FriendTeamInc/JukeBox/desktop/src/config.rs

// Config

use std::{
    collections::HashMap,
    fs::{File, create_dir_all},
    path::PathBuf,
};

use jukebox_util::{peripheral::DeviceType, rgb::RgbProfile, screen::ScreenProfile};
use serde::{Deserialize, Serialize};
use uuid::Uuid;

use crate::{
    actions::{meta::MetaNoAction, types::Action},
    input::InputKey,
};

#[derive(Serialize, Deserialize, Clone, PartialEq)]
pub enum ActionIcon {
    ImageIcon(String),
    DefaultActionIcon,
}

#[derive(Serialize, Deserialize, Clone)]
pub struct ActionConfig {
    pub action: Action,
    pub icons: Vec<ActionIcon>,
}
impl Default for ActionConfig {
    fn default() -> Self {
        Self {
            action: Box::new(MetaNoAction::default()),
            icons: Default::default(),
        }
    }
}
impl PartialEq for ActionConfig {
    fn eq(&self, other: &Self) -> bool {
        self.action == other.action.clone() && self.icons == other.icons
    }
}

#[derive(Serialize, Deserialize, Clone)]
pub struct DeviceConfig {
    pub key_map: HashMap<InputKey, ActionConfig>,
    pub rgb_profile: Option<RgbProfile>,
    pub screen_profile: Option<ScreenProfile>,
}

#[derive(Serialize, Deserialize, Clone)]
pub struct DeviceInfo {
    pub device_type: DeviceType,
    pub nickname: String,
}

#[derive(Serialize, Deserialize, Clone)]
pub struct ProfileConfig {
    // pub profile_uuid: String,
    pub profile_name: String,
    pub device_configs: HashMap<String, DeviceConfig>,
}

#[derive(Serialize, Deserialize, Clone)]
pub struct JukeBoxConfig {
    // Profile Name -> Device UID -> Device Config
    // TODO: change profile name to uuid, store name in a separate variable
    pub profiles: HashMap<String, ProfileConfig>,

    // Device UID -> (Device Type, Device Nickname)
    pub devices: HashMap<String, DeviceInfo>,

    // Action Module ID -> Action Module Config
    pub action_module_config: HashMap<String, HashMap<String, String>>,

    // Profile Name
    // TODO: change profile name to uuid, store name in a separate variable
    pub current_profile: String,

    pub enable_splash: bool,
    pub always_save_on_exit: bool,
    pub ignore_update_notifications: bool,

    pub seen_intro_messages: bool,
}
impl Default for JukeBoxConfig {
    fn default() -> Self {
        let uuid = Uuid::new_v4().to_string();

        JukeBoxConfig {
            profiles: HashMap::from([(
                uuid.clone(),
                ProfileConfig {
                    profile_name: t!("profile_name_new", idx = 1).into(),
                    device_configs: HashMap::new(),
                },
            )]),

            devices: HashMap::new(),

            action_module_config: HashMap::new(),

            current_profile: uuid,

            enable_splash: true,
            always_save_on_exit: false,
            ignore_update_notifications: false,

            seen_intro_messages: true,
        }
    }
}
impl JukeBoxConfig {
    pub fn get_dir() -> PathBuf {
        let mut p = dirs::config_dir().expect("failed to find config directory");
        p.push("JukeBoxDesktop");
        create_dir_all(&p).expect("failed to create config directory");
        p
    }

    pub fn get_logs_dir() -> PathBuf {
        let mut p = Self::get_dir();
        p.push("logs");
        create_dir_all(&p).expect("failed to create logs directory");
        p
    }

    pub fn get_icon_dir() -> PathBuf {
        let mut p = Self::get_dir();
        p.push("icons");
        create_dir_all(&p).expect("failed to create icons directory");
        p
    }

    pub fn get_app_lock() -> PathBuf {
        let mut p = Self::get_dir();
        p.push("app.lock");
        p
    }

    fn get_path() -> PathBuf {
        let mut p = Self::get_dir();
        p.push("config.json");
        p
    }

    pub fn load() -> (Self, bool) {
        let path = Self::get_path();

        let file = match File::open(path) {
            Err(e) => {
                log::error!("failed to open config file: {}", e);
                return (JukeBoxConfig::default(), false);
            }
            Ok(f) => f,
        };

        let conf = match serde_json::from_reader(file) {
            Err(e) => {
                log::error!("failed to parse config file: {}", e);

                let paths: Vec<_> = std::fs::read_dir(Self::get_dir())
                    .unwrap()
                    .filter(|f| {
                        f.as_ref()
                            .map(|f| f.file_name().to_string_lossy().contains("config.json"))
                            .unwrap_or(false)
                    })
                    .collect();

                let mut p = Self::get_dir();
                p.push(format!("config.json.old.{}", paths.len()));

                log::error!("saving old config as {:?}...", p);

                std::fs::rename(Self::get_path(), p).expect("failed to save old config");

                return (JukeBoxConfig::default(), true);
            }
            Ok(c) => c,
        };

        // TODO: serde_validate the config?

        (conf, false)
    }

    pub fn save(&self) {
        let path = Self::get_path();
        let file = File::create(path).expect("failed to create config file");
        serde_json::to_writer_pretty(file, &self).expect("failed to write config file");
    }
}
