FriendTeamInc/JukeBox/firmware/src/uid.rs

//! Unique ID
//!
//! The UID is defined as part of the MCU's OTP, meant to "uniquely" identify
//! one device from another. This UID is used as the USB serial number, as
//! well as the the ID for distinguishing devices in the desktop software.

use core::ptr::addr_of;

use defmt::unwrap;

use embassy_rp::otp::get_chipid;

static mut UID_BYTES: [u8; 16] = [0u8; 16];

const fn num_to_hex(x: u8) -> u8 {
    match x {
        0x0 => b'0',
        0x1 => b'1',
        0x2 => b'2',
        0x3 => b'3',
        0x4 => b'4',
        0x5 => b'5',
        0x6 => b'6',
        0x7 => b'7',
        0x8 => b'8',
        0x9 => b'9',
        0xA => b'A',
        0xB => b'B',
        0xC => b'C',
        0xD => b'D',
        0xE => b'E',
        0xF => b'F',
        _ => b'?',
    }
}

pub fn setup_uid() {
    unwrap!(get_chipid())
        .to_le_bytes()
        .iter()
        .flat_map(|n| [n / 16, n % 16])
        .enumerate()
        .for_each(|(i, n)| unsafe {
            UID_BYTES[i] = num_to_hex(n);
        });
}

pub fn get_uid() -> &'static str {
    // The line below is considered bad practice.
    unsafe { core::str::from_utf8(&*addr_of!(UID_BYTES)).unwrap() }
}
